Teknosofen/EagleHagen/documentation/Images/IMG_1771.jpg

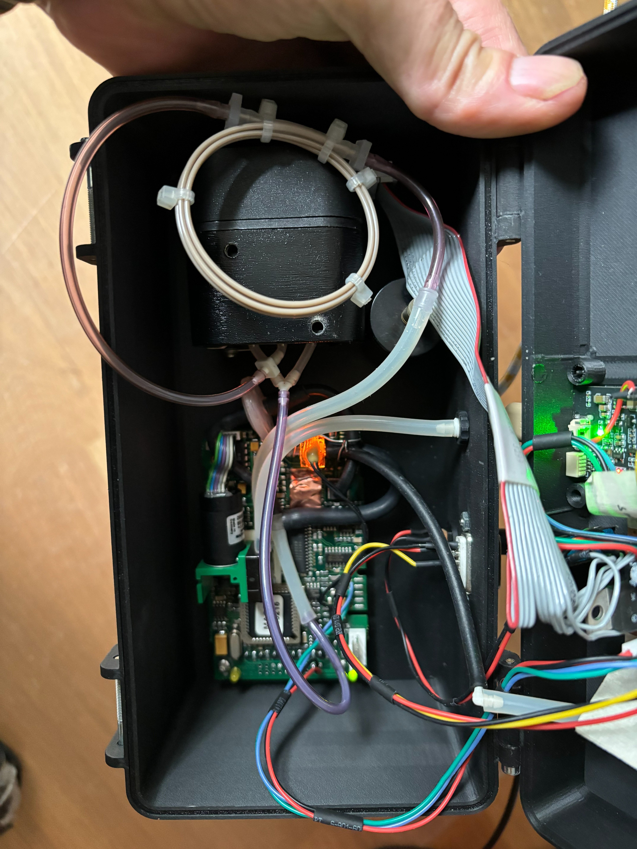
documentation/Images/IMG_1771.jpg
