Teknosofen/EagleHagen/documentation/Images/IMG_1772.jpg

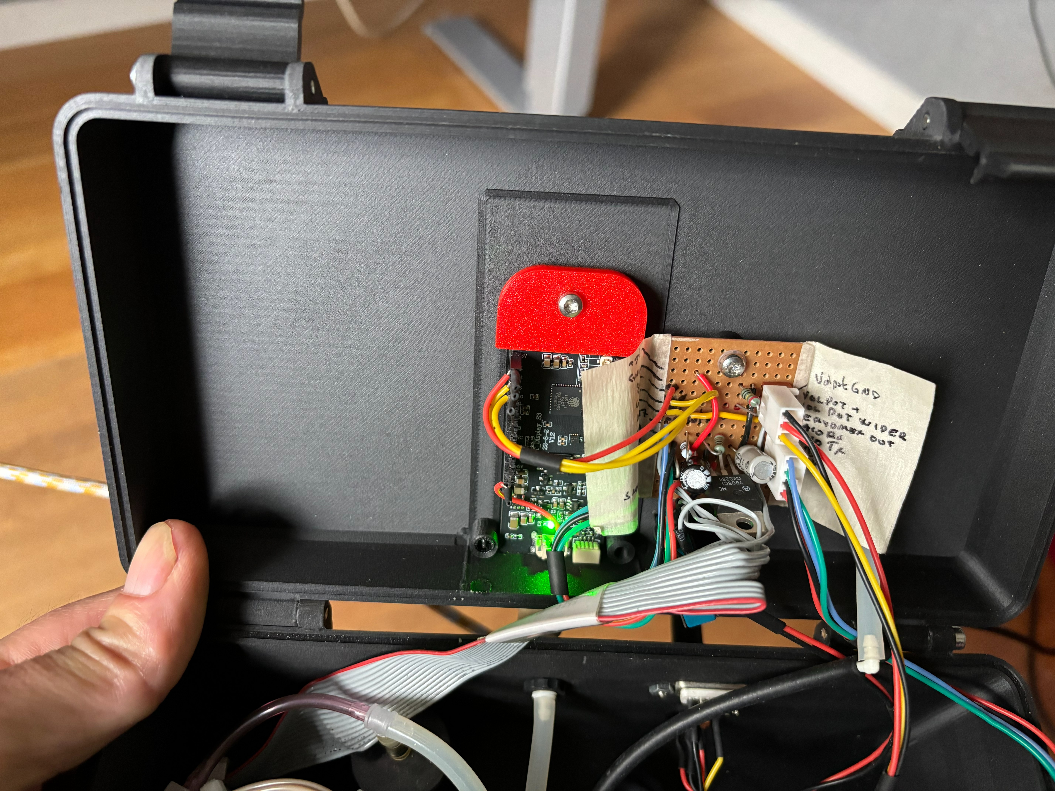
documentation/Images/IMG_1772.jpg
