Teknosofen/EagleHagen/src/WiFiManager.cpp

// WiFiManager.cpp
// Implementation of WiFi and web server management

#include "WiFiManager.h"
#include "ChartJS.h"
#include "MonitorPage.h"
#include "DebugLog.h"
#include <ESPmDNS.h>

// Store pointer for static callback
static WiFiManager* _instance = nullptr;

WiFiManager::WiFiManager(uint16_t port)
    : _server(nullptr)
    , _ws(nullptr)
    , _port(port)
    , _isAP(false)
    , _serverRunning(false)
    , _cmdQueueHead(0)
    , _cmdQueueTail(0)
    , _dataLogger(nullptr)
    , _dnsRunning(false)
{
    _instance = this;
    memset(_cmdQueue, 0, sizeof(_cmdQueue));
}

WiFiManager::~WiFiManager() {
    stopServer();
    if (_server) delete _server;
    if (_ws) delete _ws;
}

bool WiFiManager::beginAP(const char* ssid, const char* password) {
    DebugOut.println("Starting WiFi Access Point...");
    
    _isAP = true;
    
    // Start AP with or without password
    bool success;
    if (password && strlen(password) > 0) {
        success = WiFi.softAP(ssid, password);
    } else {
        success = WiFi.softAP(ssid);
    }
    
    if (!success) {
        DebugOut.println("Failed to start AP");
        return false;
    }
    
    IPAddress ip = WiFi.softAPIP();
    DebugOut.printf("AP Started: SSID='%s'\n", ssid);
    DebugOut.printf("IP Address: %s\n", ip.toString().c_str());
    
    return true;
}

bool WiFiManager::beginStation(const char* ssid, const char* password, unsigned long timeout_ms) {
    DebugOut.printf("Connecting to WiFi: %s\n", ssid);
    
    _isAP = false;
    WiFi.mode(WIFI_STA);
    WiFi.begin(ssid, password);
    
    unsigned long startTime = millis();
    while (WiFi.status() != WL_CONNECTED && (millis() - startTime) < timeout_ms) {
        delay(500);
        DebugOut.print(".");
    }
    DebugOut.println();
    
    if (WiFi.status() != WL_CONNECTED) {
        DebugOut.println("Failed to connect to WiFi");
        return false;
    }
    
    DebugOut.printf("Connected! IP: %s\n", WiFi.localIP().toString().c_str());
    return true;
}

bool WiFiManager::startServer() {
    if (_serverRunning) {
        DebugOut.println("Server already running");
        return true;
    }
    
    // Create server and WebSocket
    _server = new AsyncWebServer(_port);
    _ws = new AsyncWebSocket("/ws");
    
    // Attach WebSocket to server
    _ws->onEvent([](AsyncWebSocket* server, AsyncWebSocketClient* client,
                   AwsEventType type, void* arg, uint8_t* data, size_t len) {
        if (_instance) {
            _instance->onWebSocketEvent(server, client, type, arg, data, len);
        }
    });
    _server->addHandler(_ws);
    
    // Setup routes
    _server->on("/", HTTP_GET, [this](AsyncWebServerRequest* request) {
        handleRoot(request);
    });
    
    _server->on("/data", HTTP_GET, [this](AsyncWebServerRequest* request) {
        handleData(request);
    });
    
    _server->on("/command", HTTP_POST, [this](AsyncWebServerRequest* request) {
        handleCommand(request);
    });
    
    _server->on("/api/setFormat", HTTP_GET, [this](AsyncWebServerRequest* request) {
        handleSetFormat(request);
    });

    // Serve Chart.js from embedded gzip data (no internet required)
    _server->on("/chart.min.js", HTTP_GET, [](AsyncWebServerRequest* request) {
        AsyncWebServerResponse* response = request->beginResponse(200, "application/javascript", CHARTJS_GZ, CHARTJS_GZ_LEN);
        response->addHeader("Content-Encoding", "gzip");
        response->addHeader("Cache-Control", "public, max-age=31536000");
        request->send(response);
    });

    // Stand-alone PC monitor page (tools/Eaglehagen_Serial_Monitor.html), offered as a download.
    // It can't run from here: Web Serial needs a secure context, so it must be opened as a local file.
    _server->on("/monitor.html", HTTP_GET, [](AsyncWebServerRequest* request) {
        AsyncWebServerResponse* response = request->beginResponse(200, "text/html", MONITOR_PAGE_GZ, MONITOR_PAGE_GZ_LEN);
        response->addHeader("Content-Encoding", "gzip");
        response->addHeader("Content-Disposition", "attachment; filename=\"Eaglehagen_Serial_Monitor.html\"");
        response->addHeader("Cache-Control", "no-cache");
        request->send(response);
    });

    _server->onNotFound([this](AsyncWebServerRequest* request) {
        handleNotFound(request);
    });
    
    // Start server
    _server->begin();
    _serverRunning = true;
    
    DebugOut.println("Web server started");
    return true;
}

bool WiFiManager::beginHostname(const char* hostname) {
    String fqdn = String(hostname) + ".local";

    // mDNS: resolves <hostname>.local on Windows, macOS, iOS and Linux
    bool mdnsOk = MDNS.begin(hostname);
    if (mdnsOk) {
        MDNS.addService("http", "tcp", _port);
        DebugOut.printf("mDNS started: http://%s\n", fqdn.c_str());
    } else {
        DebugOut.println("mDNS failed to start");
    }

    // Many Android devices send .local lookups to the network's DNS server instead of
    // using mDNS. The AP hands out its own IP as DNS server, so answer that one name here.
    // Other names get "no such domain", which avoids triggering captive-portal pop-ups.
    if (_isAP) {
        _dnsServer.setErrorReplyCode(DNSReplyCode::NonExistentDomain);
        _dnsRunning = _dnsServer.start(53, fqdn, WiFi.softAPIP());
        DebugOut.printf("DNS responder for %s %s\n", fqdn.c_str(), _dnsRunning ? "started" : "failed");
    }

    return mdnsOk || _dnsRunning;
}

void WiFiManager::stopServer() {
    if (_server && _serverRunning) {
        _server->end();
        _serverRunning = false;
        DebugOut.println("Web server stopped");
    }
}

void WiFiManager::update(const CO2Data& data) {
    if (!_serverRunning) return;
    
    // Broadcast to all WebSocket clients
    String json = dataToJson(data);
    _ws->textAll(json);
}

void WiFiManager::loop() {
    if (_ws) {
        _ws->cleanupClients();
    }
    if (_dnsRunning) {
        _dnsServer.processNextRequest();  // No-op on async (core 3.x) DNSServer
    }
}

bool WiFiManager::hasClients() const {
    return _ws && _ws->count() > 0;
}

uint16_t WiFiManager::getClientCount() const {
    return _ws ? _ws->count() : 0;
}

IPAddress WiFiManager::getIP() const {
    return _isAP ? WiFi.softAPIP() : WiFi.localIP();
}

bool WiFiManager::hasCommand() {
    return _cmdQueueHead != _cmdQueueTail;
}

uint8_t WiFiManager::getCommand() {
    if (!hasCommand()) return 0;
    
    uint8_t cmd = _cmdQueue[_cmdQueueTail];
    _cmdQueueTail = (_cmdQueueTail + 1) % CMD_QUEUE_SIZE;
    return cmd;
}

void WiFiManager::handleRoot(AsyncWebServerRequest* request) {
    request->send(200, "text/html", getIndexHTML());
}

void WiFiManager::handleData(AsyncWebServerRequest* request) {
    // Return last known data (stored in update())
    // For now, return empty - real data comes via WebSocket
    request->send(200, "application/json", "{\"status\":\"use websocket\"}");
}

void WiFiManager::handleCommand(AsyncWebServerRequest* request) {
    if (!request->hasParam("cmd", true)) {
        request->send(400, "text/plain", "Missing 'cmd' parameter");
        return;
    }
    
    String cmdStr = request->getParam("cmd", true)->value();
    uint8_t cmd = 0;
    
    if (cmdStr == "start_pump") {
        cmd = 0xA5;
    } else if (cmdStr == "zero_cal") {
        cmd = 0x5A;
    } else {
        request->send(400, "text/plain", "Invalid command");
        return;
    }
    
    enqueueCommand(cmd);
    request->send(200, "text/plain", "OK");
}

void WiFiManager::handleSetFormat(AsyncWebServerRequest* request) {
    if (!request->hasParam("format")) {
        request->send(400, "text/plain", "Missing 'format' parameter");
        return;
    }
    
    int format = request->getParam("format")->value().toInt();
    
    if (format < 0 || format > 1) {
        request->send(400, "text/plain", "Invalid format (0=Legacy, 1=TabSep)");
        return;
    }
    
    // Set format via external reference (passed to WiFiManager)
    if (_dataLogger) {
        _dataLogger->setOutputFormat(format == 0 ? FORMAT_LEGACY_LABVIEW : FORMAT_TAB_SEPARATED);
        DebugOut.printf("Output format changed to: %s\n", 
                     format == 0 ? "Legacy LabVIEW" : "Tab-Separated ASCII");
        request->send(200, "text/plain", "OK");
    } else {
        request->send(500, "text/plain", "DataLogger not available");
    }
}

void WiFiManager::handleNotFound(AsyncWebServerRequest* request) {
    request->send(404, "text/plain", "Not found");
}

void WiFiManager::onWebSocketEvent(AsyncWebSocket* server, AsyncWebSocketClient* client,
                                   AwsEventType type, void* arg, uint8_t* data, size_t len) {
    switch (type) {
        case WS_EVT_CONNECT:
            DebugOut.printf("WebSocket client #%u connected from %s\n", 
                         client->id(), client->remoteIP().toString().c_str());
            break;
            
        case WS_EVT_DISCONNECT:
            DebugOut.printf("WebSocket client #%u disconnected\n", client->id());
            break;
            
        case WS_EVT_DATA: {
            // Handle incoming messages (commands from web interface)
            AwsFrameInfo* info = (AwsFrameInfo*)arg;
            if (info->final && info->index == 0 && info->len == len && info->opcode == WS_TEXT) {
                data[len] = 0;  // Null terminate
                String msg = (char*)data;
                
                // Parse JSON command
                JsonDocument doc;
                DeserializationError error = deserializeJson(doc, msg);

                if (!error && doc["cmd"].is<const char*>()) {
                    String cmd = doc["cmd"];
                    if (cmd == "start_pump") {
                        enqueueCommand(0xA5);
                    } else if (cmd == "zero_cal") {
                        enqueueCommand(0x5A);
                    }
                }
            }
            break;
        }
        
        default:
            break;
    }
}

String WiFiManager::dataToJson(const CO2Data& data) {
    JsonDocument doc;
    
    doc["timestamp"] = data.timestamp;
    doc["co2_waveform"] = data.co2_waveform;
    doc["fetco2"] = data.fetco2;
    doc["fco2"] = data.fco2;
    doc["rr"] = data.respiratory_rate;
    doc["o2_percent"] = data.o2_percent;
    doc["volume_ml"] = data.volume_ml;
    doc["status1"] = data.status1;
    doc["status2"] = data.status2;
    doc["valid"] = data.valid;
    
    // Status flags (bit=0 means OK for pump, bit=1 means problem for leak/occlusion)
    doc["pump_running"] = (data.status2 & 0x01) == 0;  // 0=running, 1=stopped
    doc["leak_detected"] = (data.status2 & 0x02) != 0;
    doc["occlusion_detected"] = (data.status2 & 0x04) != 0;

    // Current host output format, so the web page can show the real setting
    if (_dataLogger) {
        doc["output_format"] = (int)_dataLogger->getOutputFormat();  // 0=Legacy, 1=TabSep
    }
    
    String output;
    serializeJson(doc, output);
    return output;
}

void WiFiManager::enqueueCommand(uint8_t cmd) {
    uint8_t nextHead = (_cmdQueueHead + 1) % CMD_QUEUE_SIZE;
    if (nextHead != _cmdQueueTail) {
        _cmdQueue[_cmdQueueHead] = cmd;
        _cmdQueueHead = nextHead;
        DebugOut.printf("Command enqueued: 0x%02X\n", cmd);
    } else {
        DebugOut.println("Command queue full!");
    }
}

// HTML page with embedded CSS and JavaScript
String WiFiManager::getIndexHTML() {
    return R"rawliteral(
<!DOCTYPE html>
<html>
<head>
    <meta charset="UTF-8">
    <meta name="viewport" content="width=device-width, initial-scale=1.0">
    <title>Örnhagens Monitor</title>
    <style>
        * {
            margin: 0;
            padding: 0;
            box-sizing: border-box;
        }

        body {
            font-family: 'Segoe UI', Tahoma, Geneva, Verdana, sans-serif;
            background: #84B6D6;
            min-height: 100vh;
            padding: 15px;
        }

        .container {
            max-width: 1200px;
            margin: 0 auto;
            background: #f0f4f8;
            border-radius: 12px;
            box-shadow: 0 10px 40px rgba(0,0,0,0.2);
            padding: 15px 20px;
        }

        .header-row {
            display: flex;
            justify-content: space-between;
            align-items: center;
            margin-bottom: 12px;
            flex-wrap: wrap;
            gap: 8px;
        }

        h1 {
            color: #184D7B;
            font-size: 1.4em;
            margin: 0;
            display: flex;
            align-items: center;
        }

        .header-right {
            display: flex;
            align-items: center;
            gap: 10px;
        }

        .status-badge {
            padding: 2px 6px;
            border-radius: 8px;
            font-size: 0.65em;
            font-weight: bold;
            white-space: nowrap;
        }

        .status-badge.connected {
            background: #5AB66B;
            color: white;
        }

        .status-badge.disconnected {
            background: #e57373;
            color: white;
        }

        .status-badge.status-ok {
            background: #5AB66B;
            color: white;
        }

        .status-badge.status-error {
            background: #e57373;
            color: white;
            animation: pulse 2s infinite;
        }

        .byline {
            font-size: 0.7em;
            color: #5292BD;
            font-style: italic;
        }

        .metrics-grid {
            display: grid;
            grid-template-columns: repeat(auto-fit, minmax(140px, 1fr));
            gap: 10px;
            margin-bottom: 15px;
        }

        .metric-card {
            background: linear-gradient(135deg, #5292BD 0%, #3951BD 100%);
            color: white;
            padding: 8px 10px;
            border-radius: 8px;
            box-shadow: 0 3px 6px rgba(0,0,0,0.15);
            text-align: center;
        }

        .metric-label {
            font-size: 0.7em;
            opacity: 0.95;
            margin-bottom: 2px;
        }

        .metric-value {
            font-size: 1.5em;
            font-weight: bold;
        }

        .metric-unit {
            display: none;
        }
        
        .chart-container {
            background: #f8f9fa;
            border-radius: 8px;
            padding: 12px 15px;
            margin-bottom: 12px;
        }

        .chart-title {
            font-size: 1em;
            color: #184D7B;
            margin-bottom: 8px;
            font-weight: 600;
        }

        canvas {
            width: 100% !important;
            height: auto !important;
            max-height: 200px;
        }
        
        @keyframes pulse {
            0%, 100% { opacity: 1; }
            50% { opacity: 0.7; }
        }

        .controls {
            display: flex;
            gap: 10px;
            justify-content: center;
            flex-wrap: wrap;
        }

        button {
            padding: 8px 16px;
            font-size: 0.85em;
            font-weight: 600;
            border: none;
            border-radius: 5px;
            cursor: pointer;
            transition: all 0.2s;
            box-shadow: 0 2px 4px rgba(0,0,0,0.1);
        }

        .btn-primary {
            background: #184D7B;
            color: white;
        }

        .btn-primary:hover {
            background: #29697B;
            box-shadow: 0 4px 8px rgba(0,0,0,0.2);
        }

        .btn-primary:active {
            transform: scale(0.98);
        }

        .btn-secondary {
            background: #5292BD;
            color: white;
        }

        .btn-secondary:hover {
            background: #3951BD;
            box-shadow: 0 4px 8px rgba(0,0,0,0.2);
        }
        
        @media (max-width: 768px) {
            .container {
                padding: 15px;
            }
            
            h1 {
                font-size: 1.5em;
            }
            
            .metric-value {
                font-size: 2em;
            }
        }
    </style>
</head>
<body>
    <div class="container">
        <div class="header-row">
            <h1>
                <img src="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" alt="Örnhagen Logo" style="height: 40px; vertical-align: middle; margin-right: 15px;" />
                Örnhagens Monitor
            </h1>
            <div class="header-right">
                <span class="byline">by Teknosofen</span>
                <div id="connectionStatus" class="status-badge disconnected">Connecting...</div>
                <div id="pumpStatus" class="status-badge status-ok">Pump</div>
                <div id="leakStatus" class="status-badge status-ok">Leak</div>
                <div id="occlusionStatus" class="status-badge status-ok">Occl</div>
            </div>
        </div>

        <!-- Instant Values -->
        <div class="metrics-grid">
            <div class="metric-card">
                <div class="metric-label">End-Tidal CO₂ [kPa]</div>
                <div class="metric-value" id="fetco2">--</div>
            </div>

            <div class="metric-card">
                <div class="metric-label">CO₂ [kPa]</div>
                <div class="metric-value" id="fco2">--</div>
            </div>

            <div class="metric-card">
                <div class="metric-label">RR [bpm]</div>
                <div class="metric-value" id="rr">--</div>
            </div>

            <div class="metric-card">
                <div class="metric-label">O₂ [%]</div>
                <div class="metric-value" id="o2">--</div>
            </div>

            <div class="metric-card">
                <div class="metric-label">Volume [mL]</div>
                <div class="metric-value" id="volume">--</div>
            </div>
        </div>

        <!-- Charts -->
        <div class="chart-container">
            <div class="chart-title">CO₂ Waveform</div>
            <canvas id="co2Chart"></canvas>
        </div>

        <div class="chart-container">
            <div class="chart-title">O₂</div>
            <canvas id="o2Chart"></canvas>
        </div>

        <div class="chart-container">
            <div class="chart-title">Volume</div>
            <canvas id="volumeChart"></canvas>
        </div>

        <!-- Controls -->
        <div class="controls">
            <button class="btn-primary" onclick="sendCommand('start_pump')">
                Start Pump
            </button>
            <button class="btn-secondary" onclick="sendCommand('zero_cal')">
                Zero Calibration
            </button>
            <button class="btn-primary" onclick="saveDataCSV()">
                Save Data (CSV)
            </button>
            <button class="btn-primary" onclick="saveDataJSON()">
                Save Data (JSON)
            </button>
            <button class="btn-secondary" onclick="clearData()">
                Clear Data
            </button>
        </div>
        
        <!-- Output Format Selection -->
        <div style="margin: 12px auto; max-width: 550px; padding: 10px; background: #f5f5f5; border-radius: 6px;">
            <div style="font-weight: bold; margin-bottom: 8px; color: #184D7B; font-size: 0.85em;">USB Host Output Format (10 Hz)</div>
            <div style="display: flex; gap: 10px; align-items: center;">
                <label style="flex: 1; cursor: pointer; padding: 8px; background: white; border: 2px solid #ddd; border-radius: 4px; font-size: 0.85em;">
                    <input type="radio" name="outputFormat" id="formatLegacy" value="legacy" onchange="setOutputFormat(0)">
                    <strong>Legacy (LabVIEW)</strong><br>
                    <small style="color: #666;">PIC-compatible frames for LabVIEW</small>
                </label>
                <label style="flex: 1; cursor: pointer; padding: 8px; background: white; border: 2px solid #ddd; border-radius: 4px; font-size: 0.85em;">
                    <input type="radio" name="outputFormat" id="formatTabSep" value="tabsep" onchange="setOutputFormat(1)">
                    <strong>Tab-Separated ASCII</strong><br>
                    <small style="color: #666;">CO2 kPa, O2 %, RR, Volume, Status</small>
                </label>
            </div>
        </div>

        <div style="text-align: center; margin-top: 12px; color: #5292BD; font-size: 0.8em;">
            <div>Data Points: <span id="dataCount">0</span> / 960 (2 min buffer) | Duration: <span id="duration">0:00</span></div>
        </div>

        <!-- PC monitor page download (stand-alone page for USB use) -->
        <div style="margin: 14px auto 0; max-width: 550px; padding: 10px 12px; background: #f5f5f5; border-radius: 6px; font-size: 0.85em; display: flex; align-items: center; gap: 12px;">
            <div style="flex: 1; color: #555;">
                <strong style="color: #184D7B;">PC monitor page (USB)</strong><br>
                Save it on a PC, then open it in Chrome or Edge to view and record data over the USB cable. Accepts both output formats.
            </div>
            <a href="/monitor.html" download="Eaglehagen_Serial_Monitor.html" class="btn-secondary"
               style="text-decoration: none; padding: 8px 14px; border-radius: 6px; white-space: nowrap;">Download</a>
        </div>
    </div>
    
    <script src="/chart.min.js"></script>
    <script>
        // WebSocket connection
        let ws;
        let reconnectInterval;
        
        // Chart configuration
        const maxDataPoints = 960; // 2 minutes at 8 Hz (8 * 60 * 2)
        
        // Chart.js instances
        let co2Chart, o2Chart, volumeChart;
        
        // Data buffers
        let co2Data = [];
        let o2Data = [];
        let volumeData = [];
        let timeLabels = [];
        
        // Complete data storage for export (includes all received data)
        let dataLog = [];
        let recordingStartTime = null;
        
        function initWebSocket() {
            const protocol = window.location.protocol === 'https:' ? 'wss:' : 'ws:';
            const wsUrl = `${protocol}//${window.location.host}/ws`;
            
            ws = new WebSocket(wsUrl);
            
            ws.onopen = function() {
                console.log('WebSocket connected');
                updateConnectionStatus(true);
                if (reconnectInterval) {
                    clearInterval(reconnectInterval);
                    reconnectInterval = null;
                }
            };
            
            ws.onclose = function() {
                console.log('WebSocket disconnected');
                updateConnectionStatus(false);
                // Attempt to reconnect every 3 seconds
                if (!reconnectInterval) {
                    reconnectInterval = setInterval(initWebSocket, 3000);
                }
            };
            
            ws.onerror = function(error) {
                console.error('WebSocket error:', error);
            };
            
            ws.onmessage = function(event) {
                try {
                    const data = JSON.parse(event.data);
                    updateDisplay(data);
                } catch (e) {
                    console.error('Error parsing data:', e);
                }
            };
        }
        
        function updateConnectionStatus(connected) {
            const statusDiv = document.getElementById('connectionStatus');
            if (connected) {
                statusDiv.className = 'status-badge connected';
                statusDiv.textContent = 'Connected';
            } else {
                statusDiv.className = 'status-badge disconnected';
                statusDiv.textContent = 'Reconnecting...';
            }
        }
        
        function updateDisplay(data) {
            // Update instant values
            document.getElementById('fetco2').textContent = ((data.fetco2 || 0) * 0.133322).toFixed(1);
            document.getElementById('fco2').textContent = ((data.co2_waveform || 0) * 0.133322).toFixed(1);
            document.getElementById('rr').textContent = data.rr || '--';
            document.getElementById('o2').textContent = data.o2_percent ? data.o2_percent.toFixed(1) : '--';
            document.getElementById('volume').textContent = data.volume_ml ? Math.round(data.volume_ml) : '--';
            
            // Update status indicators
            updateStatus('pumpStatus', data.pump_running, 'Pump', 'Pump!');
            updateStatus('leakStatus', !data.leak_detected, 'Leak', 'Leak!');
            updateFormatSelection(data.output_format);
            updateStatus('occlusionStatus', !data.occlusion_detected, 'Occl', 'Occl!');
            
            // Get current time
            const now = new Date();
            const timeStr = now.toLocaleTimeString();
            
            // Store complete data for export
            if (!recordingStartTime) {
                recordingStartTime = now;
            }
            
            dataLog.push({
                timestamp: now.toISOString(),
                elapsed_seconds: (now - recordingStartTime) / 1000,
                co2_waveform: (data.co2_waveform || 0) * 0.133322,
                fetco2: (data.fetco2 || 0) * 0.133322,
                fco2: (data.fco2 || 0) * 0.133322,
                rr: data.rr || 0,
                o2_percent: data.o2_percent || 0,
                volume_ml: data.volume_ml || 0,
                pump_running: data.pump_running || false,
                leak_detected: data.leak_detected || false,
                occlusion_detected: data.occlusion_detected || false,
                status1: data.status1 || 0,
                status2: data.status2 || 0
            });
            
            // Update chart data
            co2Data.push((data.co2_waveform || 0) * 0.133322);  // Convert mmHg to kPa
            o2Data.push(data.o2_percent || 0);
            volumeData.push(data.volume_ml || 0);
            timeLabels.push(timeStr);
            
            // Keep only last maxDataPoints in charts
            if (co2Data.length > maxDataPoints) {
                co2Data.shift();
                o2Data.shift();
                volumeData.shift();
                timeLabels.shift();
            }
            
            // Keep only last maxDataPoints in dataLog
            if (dataLog.length > maxDataPoints) {
                dataLog.shift();
            }
            
            // Update counters
            document.getElementById('dataCount').textContent = dataLog.length;
            
            const elapsed = (now - recordingStartTime) / 1000;
            const minutes = Math.floor(elapsed / 60);
            const seconds = Math.floor(elapsed % 60);
            document.getElementById('duration').textContent = `${minutes}:${seconds.toString().padStart(2, '0')}`;
            
            updateCharts();
        }
        
        function updateStatus(elementId, isOk, okText, errorText) {
            const element = document.getElementById(elementId);
            if (isOk) {
                element.className = 'status-badge status-ok';
                element.textContent = okText;
            } else {
                element.className = 'status-badge status-error';
                element.textContent = errorText;
            }
        }
        
        function updateCharts() {
            co2Chart.data.labels = timeLabels;
            co2Chart.data.datasets[0].data = co2Data;
            co2Chart.update('none'); // Update without animation for performance
            
            o2Chart.data.labels = timeLabels;
            o2Chart.data.datasets[0].data = o2Data;
            o2Chart.update('none');
            
            volumeChart.data.labels = timeLabels;
            volumeChart.data.datasets[0].data = volumeData;
            volumeChart.update('none');
        }
        
        function sendCommand(cmd) {
            if (ws && ws.readyState === WebSocket.OPEN) {
                const message = JSON.stringify({ cmd: cmd });
                ws.send(message);
                console.log('Command sent:', cmd);
            } else {
                alert('Not connected to sensor');
            }
        }
        
        // Reflect the device's actual format (it can also be changed with the BOOT button)
        function updateFormatSelection(format) {
            if (format === undefined) return;
            document.getElementById('formatLegacy').checked = (format === 0);
            document.getElementById('formatTabSep').checked = (format === 1);
        }

        function setOutputFormat(format) {
            fetch('/api/setFormat?format=' + format)
                .then(response => response.text())
                .then(data => {
                    console.log('Output format changed:', format === 0 ? 'Legacy LabVIEW' : 'Tab-Separated');
                })
                .catch(error => console.error('Error setting format:', error));
        }
        
        function initCharts() {
            const chartConfig = {
                type: 'line',
                options: {
                    responsive: true,
                    maintainAspectRatio: false,
                    animation: false,
                    scales: {
                        x: {
                            display: true,
                            title: {
                                display: true,
                                text: 'Time'
                            },
                            ticks: {
                                maxRotation: 45,
                                minRotation: 45,
                                autoSkip: true,
                                maxTicksLimit: 10
                            }
                        },
                        y: {
                            beginAtZero: true
                        }
                    },
                    plugins: {
                        legend: {
                            display: false
                        }
                    },
                    elements: {
                        line: {
                            tension: 0.4
                        },
                        point: {
                            radius: 0
                        }
                    }
                }
            };
            
            // CO2 Chart
            co2Chart = new Chart(document.getElementById('co2Chart'), {
                ...chartConfig,
                data: {
                    labels: timeLabels,
                    datasets: [{
                        data: co2Data,
                        borderColor: 'rgb(102, 126, 234)',
                        backgroundColor: 'rgba(102, 126, 234, 0.1)',
                        borderWidth: 2,
                        fill: true
                    }]
                },
                options: {
                    ...chartConfig.options,
                    scales: {
                        ...chartConfig.options.scales,
                        y: {
                            ...chartConfig.options.scales.y,
                            title: {
                                display: true,
                                text: 'CO₂ Waveform (kPa)'
                            },
                            suggestedMin: 0,
                            suggestedMax: 8
                        }
                    }
                }
            });
            
            // O2 Chart
            o2Chart = new Chart(document.getElementById('o2Chart'), {
                ...chartConfig,
                data: {
                    labels: timeLabels,
                    datasets: [{
                        data: o2Data,
                        borderColor: 'rgb(75, 192, 192)',
                        backgroundColor: 'rgba(75, 192, 192, 0.1)',
                        borderWidth: 2,
                        fill: true
                    }]
                },
                options: {
                    ...chartConfig.options,
                    scales: {
                        ...chartConfig.options.scales,
                        y: {
                            ...chartConfig.options.scales.y,
                            min: 0,
                            max: 100,
                            title: {
                                display: true,
                                text: 'O₂ (%)'
                            }
                        }
                    }
                }
            });
            
            // Volume Chart
            volumeChart = new Chart(document.getElementById('volumeChart'), {
                ...chartConfig,
                data: {
                    labels: timeLabels,
                    datasets: [{
                        data: volumeData,
                        borderColor: 'rgb(255, 99, 132)',
                        backgroundColor: 'rgba(255, 99, 132, 0.1)',
                        borderWidth: 2,
                        fill: true
                    }]
                },
                options: {
                    ...chartConfig.options,
                    scales: {
                        ...chartConfig.options.scales,
                        y: {
                            ...chartConfig.options.scales.y,
                            title: {
                                display: true,
                                text: 'Volume (mL)'
                            },
                            suggestedMin: 0,
                            suggestedMax: 1000
                        }
                    }
                }
            });
        }
        
        function saveDataCSV() {
            if (dataLog.length === 0) {
                alert('No data to save');
                return;
            }
            
            // Create CSV header
            let csv = 'Timestamp,Elapsed(s),CO2_Waveform(kPa),FetCO2(kPa),FiCO2(kPa),RR(bpm),O2(%),Volume(mL),Pump_Running,Leak_Detected,Occlusion_Detected,Status1,Status2\n';

            // Add data rows
            dataLog.forEach(row => {
                csv += `${row.timestamp},${row.elapsed_seconds.toFixed(3)},${row.co2_waveform.toFixed(2)},${row.fetco2.toFixed(2)},${row.fco2.toFixed(2)},${row.rr},${row.o2_percent.toFixed(2)},${row.volume_ml.toFixed(1)},${row.pump_running},${row.leak_detected},${row.occlusion_detected},${row.status1},${row.status2}\n`;
            });
            
            // Create download
            const blob = new Blob([csv], { type: 'text/csv' });
            const url = window.URL.createObjectURL(blob);
            const a = document.createElement('a');
            a.href = url;
            a.download = `medair_co2_data_${new Date().toISOString().replace(/[:.]/g, '-')}.csv`;
            document.body.appendChild(a);
            a.click();
            document.body.removeChild(a);
            window.URL.revokeObjectURL(url);
            
            console.log(`Saved ${dataLog.length} data points to CSV`);
        }
        
        function saveDataJSON() {
            if (dataLog.length === 0) {
                alert('No data to save');
                return;
            }
            
            // Create JSON structure with metadata
            const exportData = {
                metadata: {
                    export_time: new Date().toISOString(),
                    recording_start: recordingStartTime ? recordingStartTime.toISOString() : null,
                    duration_seconds: recordingStartTime ? (new Date() - recordingStartTime) / 1000 : 0,
                    data_points: dataLog.length,
                    sample_rate_hz: 8,
                    device: 'MedAir CO2 Monitor',
                    firmware: 'ESP32-S3',
                    units: {
                        co2_waveform: 'kPa',
                        fetco2: 'kPa',
                        fco2: 'kPa',
                        rr: 'bpm',
                        o2_percent: '%',
                        volume_ml: 'mL'
                    }
                },
                data: dataLog
            };
            
            // Create download
            const json = JSON.stringify(exportData, null, 2);
            const blob = new Blob([json], { type: 'application/json' });
            const url = window.URL.createObjectURL(blob);
            const a = document.createElement('a');
            a.href = url;
            a.download = `medair_co2_data_${new Date().toISOString().replace(/[:.]/g, '-')}.json`;
            document.body.appendChild(a);
            a.click();
            document.body.removeChild(a);
            window.URL.revokeObjectURL(url);
            
            console.log(`Saved ${dataLog.length} data points to JSON`);
        }
        
        function clearData() {
            if (dataLog.length === 0) {
                alert('No data to clear');
                return;
            }
            
            if (!confirm(`Clear ${dataLog.length} data points? This cannot be undone.`)) {
                return;
            }
            
            // Clear all data
            dataLog = [];
            co2Data = [];
            o2Data = [];
            volumeData = [];
            timeLabels = [];
            recordingStartTime = null;
            
            // Update counters
            document.getElementById('dataCount').textContent = '0';
            document.getElementById('duration').textContent = '0:00';
            
            // Update charts
            updateCharts();
            
            console.log('Data cleared');
        }
        
        // Initialize on page load
        window.addEventListener('load', function() {
            initCharts();
            initWebSocket();
        });
    </script>
</body>
</html>
)rawliteral";
}

String WiFiManager::getStyleCSS() {
    // CSS is embedded in HTML
    return "";
}

String WiFiManager::getAppJS() {
    // JavaScript is embedded in HTML
    return "";
}
