Teknosofen/EagleHagen/include/ChartJS.h

#ifndef CHARTJS_H
#define CHARTJS_H

#include <Arduino.h>

// Chart.js 4.4.0 minified, gzip compressed
// Original size: 205222 bytes
// Compressed size: 69376 bytes

const uint8_t PROGMEM CHARTJS_GZ[] = {
  0x1f, 0x8b, 0x08, 0x08, 0x52, 0xde, 0x7d, 0x69, 0x02, 0x03, 0x63, 0x68,
  0x61, 0x72, 0x74, 0x2e, 0x6d, 0x69, 0x6e, 0x2e, 0x6a, 0x73, 0x00, 0xd4,
  0x7d, 0x6d, 0x77, 0xdb, 0x36, 0xb3, 0xe0, 0xf7, 0xfd, 0x15, 0x36, 0x6f,
  0xe3, 0x92, 0x16, 0x44, 0x4b, 0xb2, 0xe5, 0x38, 0x94, 0x69, 0xdd, 0xc4,
  0x49, 0x9a, 0xb4, 0x49, 0xec, 0xda, 0x6e, 0xda, 0xd4, 0xf5, 0x75, 0x29,
  0x11, 0x92, 0xd0, 0x50, 0xa4, 0x4a, 0x42, 0xb1, 0x55, 0x5b, 0xff, 0x7d,
  0x67, 0x06, 0x00, 0x09, 0x4a, 0x4a, 0x9e, 0xe7, 0x9e, 0x7b, 0x76, 0xcf,
  0x6e, 0x73, 0x6a, 0x11, 0xef, 0x83, 0xc1, 0x60, 0x30, 0x18, 0x0c, 0x06,
  0x7b, 0xbb, 0xbb, 0xff, 0x6b, 0x6b, 0x77, 0xeb, 0xf2, 0xb3, 0x98, 0xcd,
  0x78, 0xbc, 0x35, 0x15, 0xa9, 0x18, 0x89, 0x61, 0x24, 0x45, 0x96, 0x6e,
  0x0d, 0xf8, 0x30, 0x9a, 0x17, 0x7c, 0x4b, 0x4e, 0xf8, 0x56, 0x96, 0x8b,
  0xb1, 0x48, 0xa3, 0x64, 0x6b, 0x24, 0x12, 0x5e, 0x6c, 0x45, 0x90, 0x3b,
  0xca, 0x8b, 0x2d, 0x99, 0x41, 0xae, 0xad, 0x28, 0xc9, 0x79, 0x14, 0x2f,
  0x74, 0x69, 0x1e, 0xfb, 0x58, 0xe5, 0x99, 0x5d, 0x22, 0xd8, 0xda, 0x4b,
  0x67, 0xd3, 0xbd, 0xe1, 0x24, 0xca, 0xa5, 0xff, 0x57, 0xf1, 0x9f, 0x07,
  0xfe, 0x81, 0xdf, 0xda, 0x8b, 0x45, 0x21, 0x75, 0xdc, 0x7c, 0x1a, 0x43,
  0x3c, 0x94, 0xc3, 0xa2, 0x2f, 0xb3, 0xad, 0x0f, 0x67, 0x57, 0x5b, 0xd8,
  0xf6, 0xe5, 0xc5, 0xdb, 0xad, 0x3b, 0x21, 0x27, 0x5b, 0xf1, 0x22, 0x8d,
  0xa6, 0x00, 0x59, 0x92, 0x2c, 0xb6, 0xc6, 0x3c, 0xe5, 0x79, 0x24, 0x01,
  0x5e, 0x82, 0x66, 0x7b, 0xeb, 0x7d, 0x96, 0xf3, 0x2d, 0x91, 0x8e, 0xb2,
  0x7c, 0x4a, 0xa0, 0x07, 0x5b, 0x13, 0x29, 0x67, 0x45, 0xb0, 0xb7, 0x77,
  0x77, 0x77, 0x07, 0xf5, 0xc6, 0x3c, 0x11, 0x5f, 0x72, 0x7f, 0x98, 0x4d,
  0xf7, 0xe6, 0x85, 0x48, 0xc7, 0xcd, 0x22, 0x17, 0x4d, 0xac, 0xb6, 0xa9,
  0xab, 0x6d, 0x52, 0x45, 0xd0, 0xf6, 0xde, 0xff, 0xda, 0xdb, 0xdd, 0x46,
  0x18, 0x4e, 0x35, 0xa8, 0x5b, 0x5f, 0x08, 0x56, 0x8c, 0xb2, 0xeb, 0x24,
  0xa8, 0xff, 0x2a, 0xfc, 0x2c, 0x1f, 0x63, 0x92, 0x3b, 0xf4, 0xb6, 0x3a,
  0xad, 0xce, 0x7e, 0x55, 0xec, 0x34, 0x4b, 0x65, 0x2e, 0x06, 0x73, 0x99,
  0xe5, 0x58, 0xef, 0xd6, 0x05, 0x4f, 0x78, 0x54, 0x00, 0xc8, 0xf3, 0x34,
  0xe6, 0x39, 0xe1, 0xf4, 0xfd, 0xdb, 0xab, 0xad, 0x77, 0x62, 0xc8, 0xd3,
  0x82, 0x53, 0xcb, 0xdb, 0xa3, 0x79, 0x3a, 0x44, 0xf0, 0x5d, 0xc9, 0xb8,
  0xf7, 0xe0, 0x64, 0x83, 0xbf, 0xf8, 0x50, 0x3a, 0x61, 0x28, 0x17, 0x33,
  0x9e, 0x8d, 0xb6, 0xf8, 0xfd, 0x2c, 0xcb, 0x65, 0xb1, 0xb3, 0xe3, 0x60,
  0x1d, 0x23, 0x91, 0xf2, 0xd8, 0xd9, 0x36, 0x89, 0xd3, 0x2c, 0x9e, 0x27,
  0xbc, 0xaf, 0x7e, 0x7c, 0x9d, 0x35, 0xe4, 0xae, 0x17, 0x38, 0xa6, 0xda,
  0xaa, 0x26, 0x55, 0x7a, 0x67, 0x47, 0xfd, 0xfa, 0xd1, 0x34, 0xee, 0xab,
  0x4f, 0x97, 0x7b, 0x81, 0x2b, 0xc3, 0x4d, 0x0d, 0x8c, 0x93, 0x6c, 0x10,
  0x25, 0x57, 0x13, 0x51, 0xf4, 0xab, 0xcf, 0x40, 0x3e, 0x3e, 0x16, 0x3c,
  0x19, 0x79, 0x3e, 0x75, 0x1c, 0xdb, 0x5b, 0xba, 0x12, 0x12, 0x98, 0x5b,
  0x76, 0x06, 0x7a, 0x82, 0x23, 0x59, 0x00, 0x3a, 0xa0, 0x37, 0xbd, 0x2f,
  0x11, 0xf4, 0x3e, 0x3c, 0xa3, 0xbe, 0xf9, 0xa3, 0x9c, 0xf3, 0x7f, 0xb8,
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
};
const unsigned int CHARTJS_GZ_LEN = 69376;

#endif // CHARTJS_H
